jmh8231-Dev/agissat-hw-2025/docs/Ref/STM32H745XI 전원설계/.@__thumb/s800STM32H745 Powet supply scheme.PNG

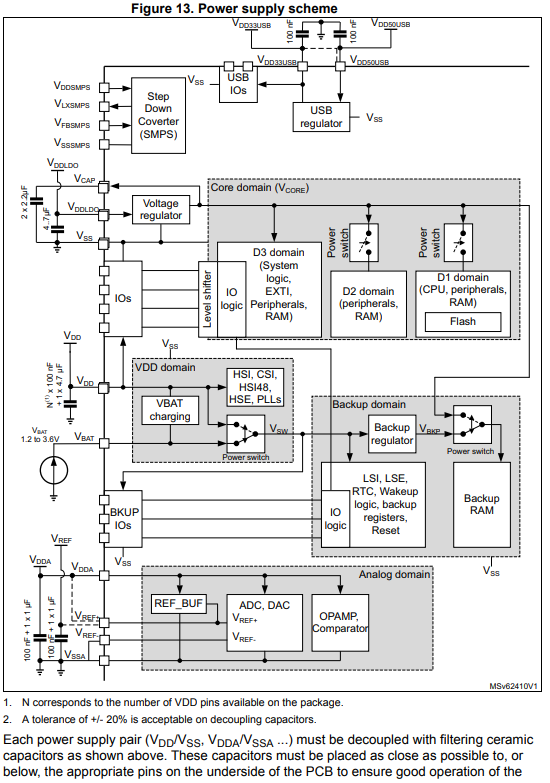
docs/Ref/STM32H745XI 전원설계/.@__thumb/s800STM32H745 Powet supply scheme.PNG
