jmh8231-Dev/agissat-hw-2025/RadCheck-SDRAM/Additional Parts.kicad_sch

## KiCad design RadCheck-SDRAM/Additional Parts.kicad_sch (2025-08-21)

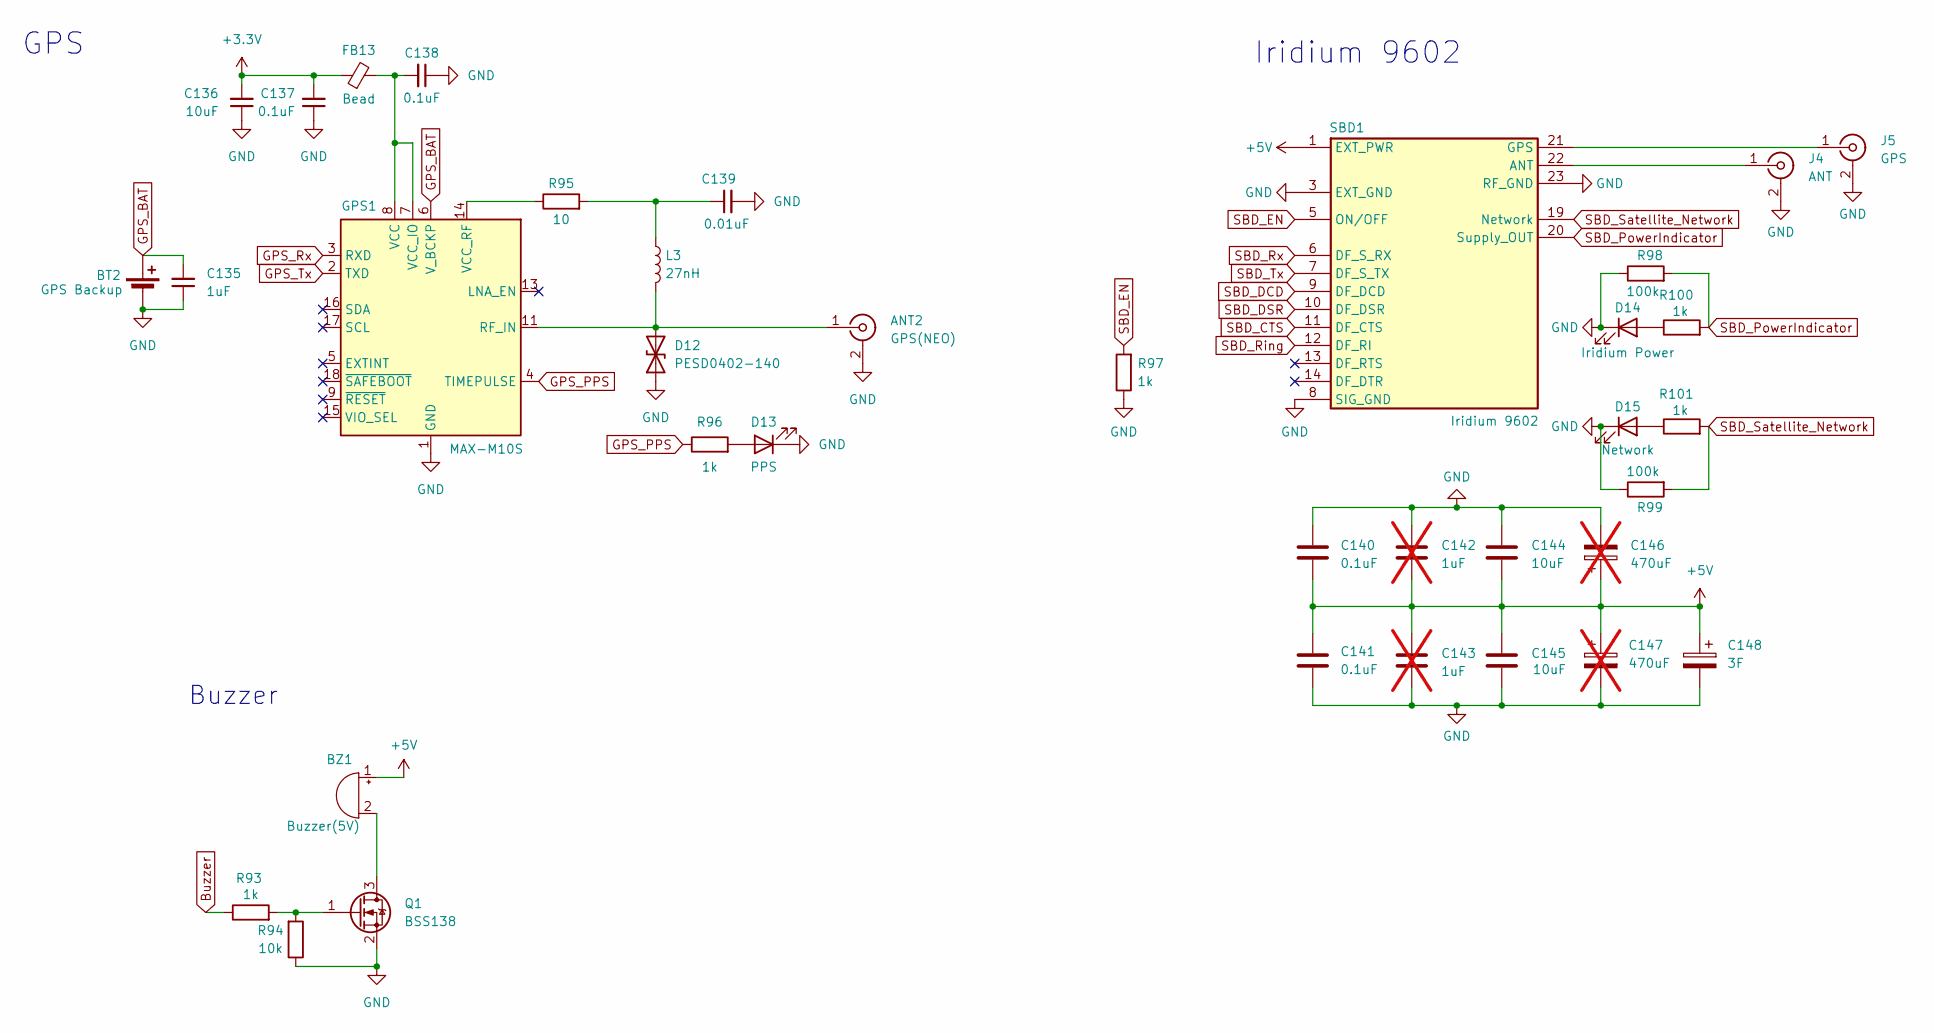
[picture p11: schematic Additional Parts.kicad_sch]

Parts:
ANT2: GPS(NEO); SMA_Amphenol_132134-11_Vertical
BT2: GPS Backup; BAT-HLD-001
BZ1: Buzzer(5V); Buzzer_12x9.5RM7.6
C135: 1uF; C_0805_2012Metric
C136: 10uF; C_1206_3216Metric
C137, C138, C140, C141: 0.1uF; C_0805_2012Metric
C139: 0.01uF; C_0805_2012Metric
C142, C143: 1uF; C_0805_2012Metric; not fitted
C144, C145: 10uF; C_1210_3225Metric
C146, C147: 470uF; MVG25WV470M; not fitted
C148: 3F; PTV-6R0H505-R
D12: PESD0402-140; D_0402_1005Metric_Pad0.77x0.64mm_HandSolder
D13: PPS; LED_0805_2012Metric
D14: Iridium Power; LED_0805_2012Metric
D15: Network; LED_0805_2012Metric
FB13: Bead; L_0805_2012Metric
GPS1: MAX-M10S; ublox_MAX
J4: ANT; SMA_Amphenol_132134-11_Vertical
J5: GPS; SMA_Amphenol_132134-11_Vertical
L3: 27nH; L_0805_2012Metric
Q1: BSS138; SOT-23
R93, R96, R97, R100, R101: 1k; R_0805_2012Metric
R94: 10k; R_0603_1608Metric
R95: 10; R_0805_2012Metric
R98, R99: 100k; R_0805_2012Metric
SBD1: Iridium 9602; Iridium_9602

Connections:
+3.3V: C136.2, C137.2, FB13.1
+5V: BZ1.1 (-), C140.2, C141.1, C142.2, C143.1, C144.2, C145.1, C146.1, C147.1, C148.1, SBD1.1 (EXT_PWR), SBD1.2 (EXT_PWR)
Buzzer: R93.1
GND: ANT2.2 (Ext), BT2.2 (-), C135.1, C136.1, C137.1, C138.1, C139.2, C140.1, C141.2, C142.1, C143.2, C144.1, C145.2, C146.2, C147.2, C148.2, D12.1 (A1), D13.1 (K), D14.1 (K), D15.1 (K), GPS1.1 (GND), GPS1.10 (GND), GPS1.12 (GND), J4.2 (Ext), J5.2 (Ext), Q1.2 (S), R94.1, R97.1, R98.1, R99.1, SBD1.3 (EXT_GND), SBD1.4 (EXT_GND), SBD1.8 (SIG_GND), SBD1.15 (SIG_GND), SBD1.18 (SIG_GND), SBD1.23 (RF_GND)
GPS_BAT: BT2.1 (+), C135.2, GPS1.6 (V_BCKP)
GPS_PPS: GPS1.4 (TIMEPULSE), R96.1
GPS_Rx: GPS1.3 (RXD)
GPS_Tx: GPS1.2 (TXD)
unnamed: ANT2.1 (In), D12.2 (A2), GPS1.11 (RF_IN), L3.2
unnamed: BZ1.2 (+), Q1.3 (D)
unnamed: C138.2, FB13.2, GPS1.7 (VCC_IO), GPS1.8 (VCC)
unnamed: C139.1, L3.1, R95.2
unnamed: D13.2 (A), R96.2
unnamed: D14.2 (A), R100.1
unnamed: D15.2 (A), R101.1
unnamed: GPS1.14 (VCC_RF), R95.1
unnamed: J4.1 (In), SBD1.22 (ANT)
unnamed: J5.1 (In), SBD1.21 (GPS)
unnamed: Q1.1 (G), R93.2, R94.2
SBD_CTS: SBD1.11 (DF_CTS)
SBD_DCD: SBD1.9 (DF_DCD)
SBD_DSR: SBD1.10 (DF_DSR)
SBD_EN: R97.2, SBD1.5 (ON/OFF)
SBD_PowerIndicator: R98.2, R100.2, SBD1.20 (Supply_OUT)
SBD_Ring: SBD1.12 (DF_RI)
SBD_Rx: SBD1.6 (DF_S_RX)
SBD_Satellite_Network: R99.2, R101.2, SBD1.19 (Network)
SBD_Tx: SBD1.7 (DF_S_TX)

Notes on the sheet:
Iridium 9602
Buzzer
GPS
