jmh8231-Dev/agissat-hw-2025/RadCheck-SDRAM/MCU.kicad_sch

## KiCad design RadCheck-SDRAM/MCU.kicad_sch (2025-08-21)

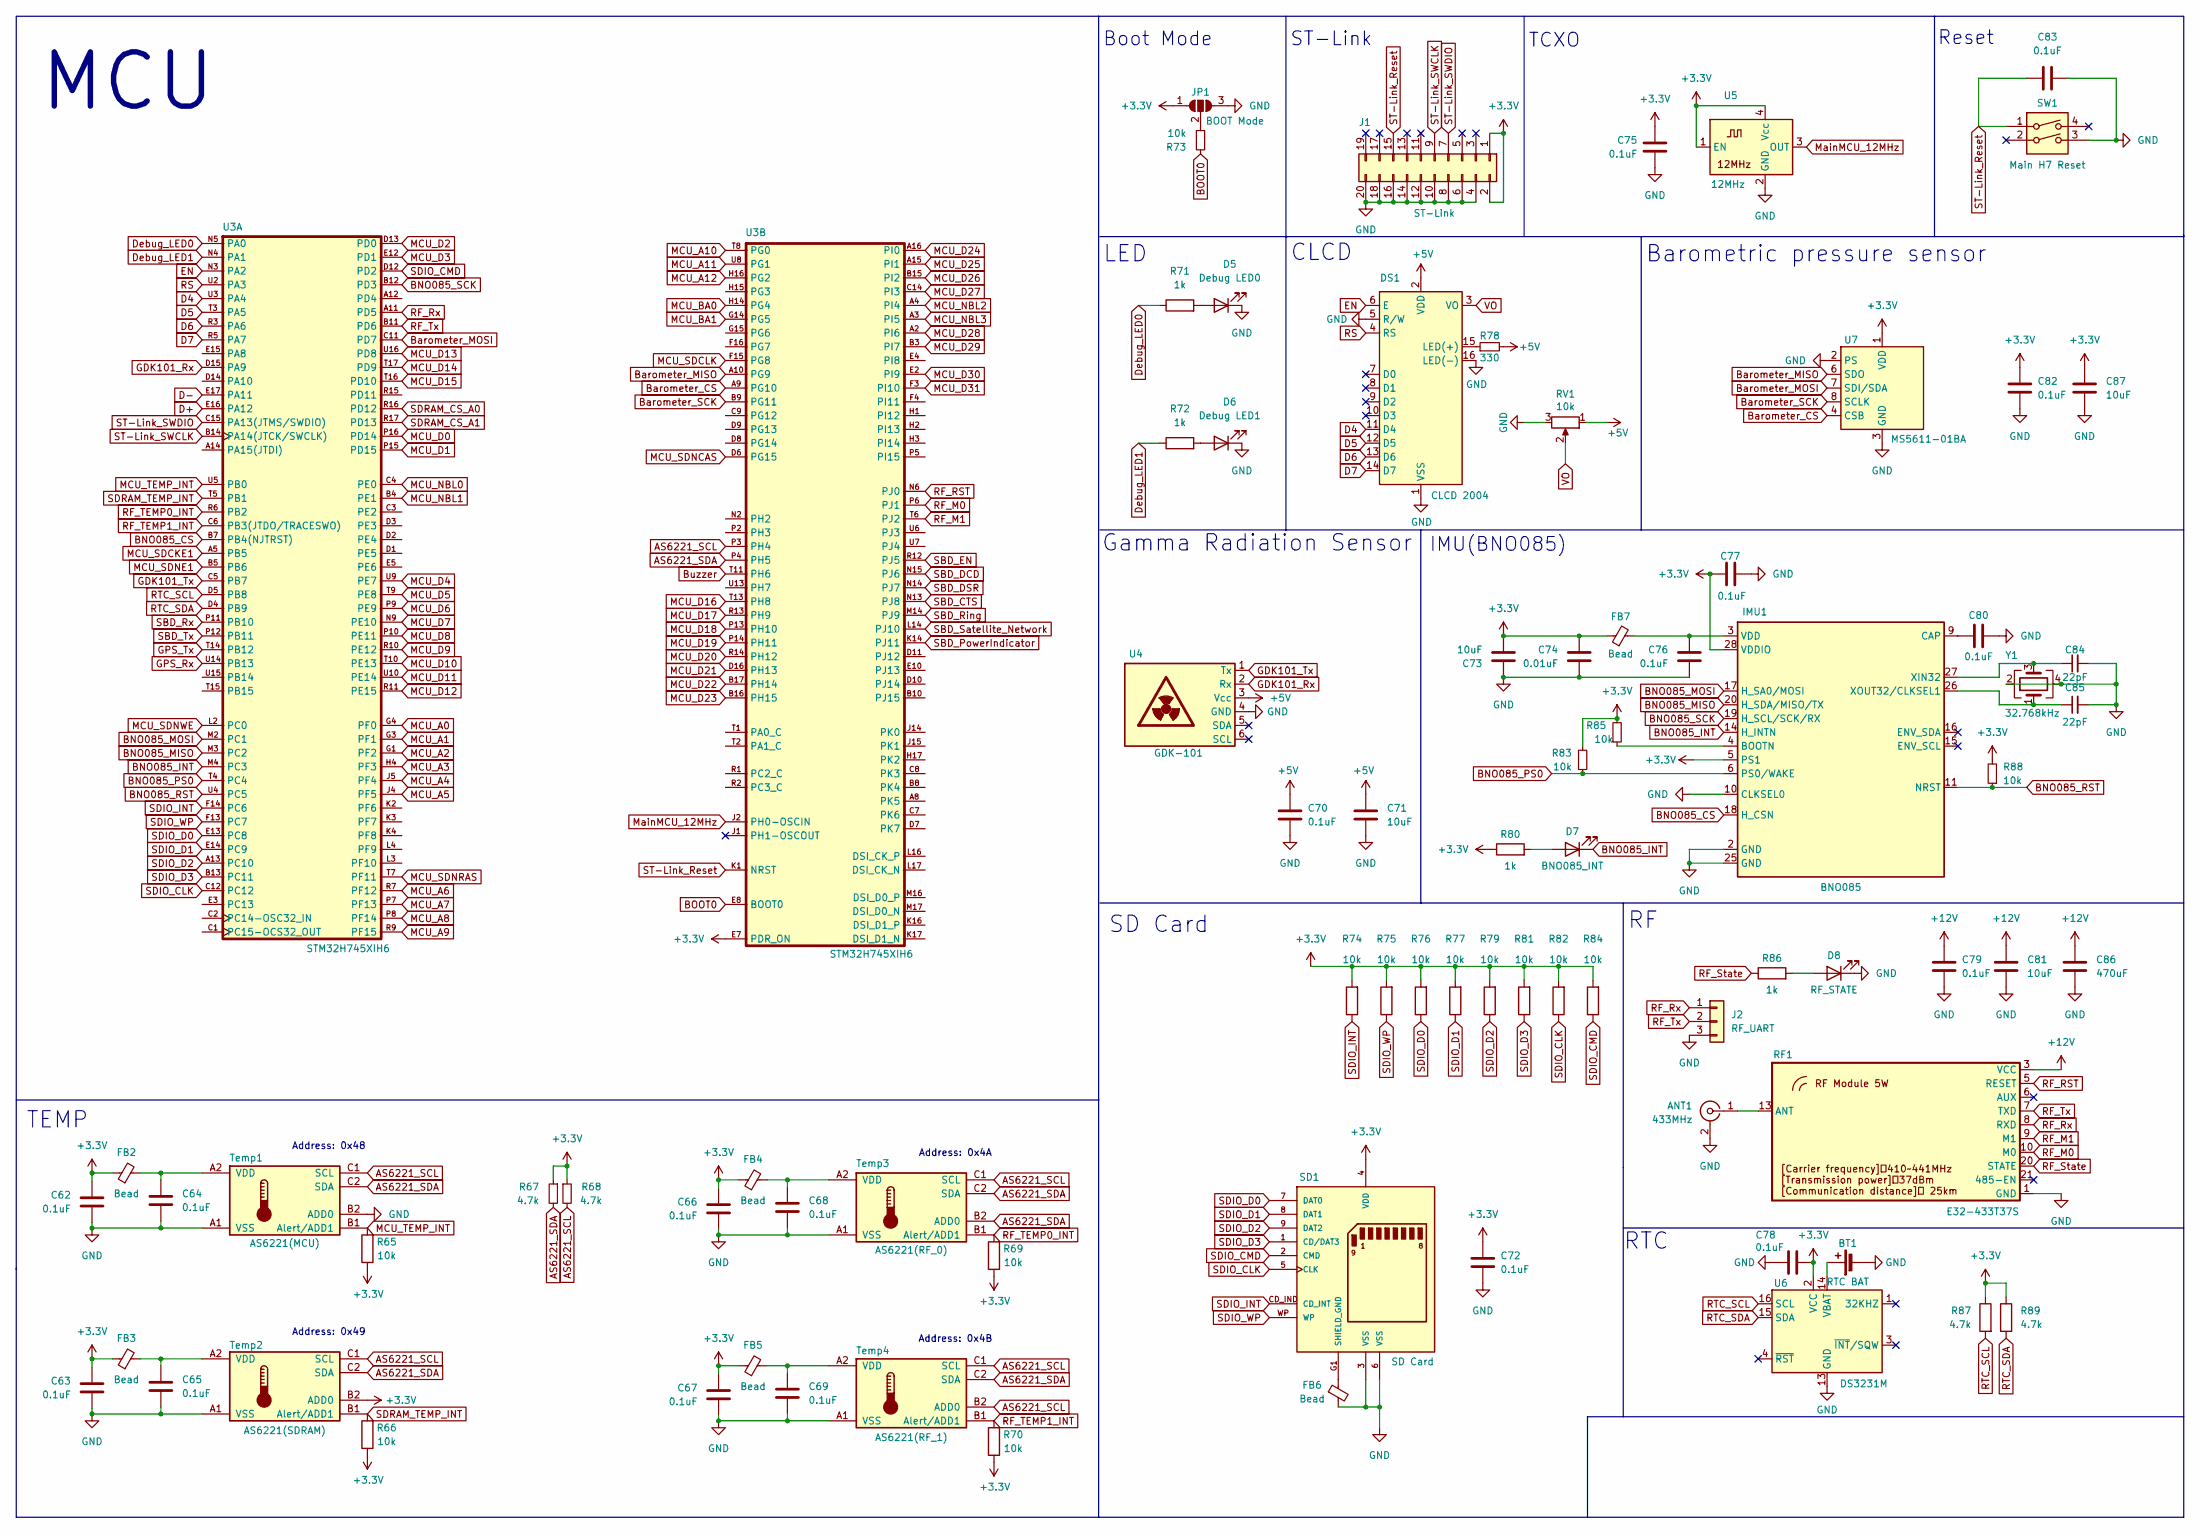
[picture p12: schematic MCU.kicad_sch]

Parts:
ANT1: 433MHz; SMA_Amphenol_132134-11_Vertical
BT1: RTC BAT; BAT-HLD-001
C62, C63, C64, C65, C66, C67, C68, C69, C70, C72, C75, C76, C77, C78, C79, C80, C82, C83: 0.1uF; C_0805_2012Metric
C71, C73, C81, C87: 10uF; C_1210_3225Metric
C74: 0.01uF; C_0805_2012Metric
C84, C85: 22pF; C_0805_2012Metric
C86: 470uF; MVG25WV470M
D5: Debug LED0; LED_0805_2012Metric
D6: Debug LED1; LED_0805_2012Metric
D7: BNO085_INT; LED_0805_2012Metric
D8: RF_STATE; LED_0805_2012Metric
DS1: CLCD 2004; LCD-20x4
FB2, FB3, FB4, FB5, FB6, FB7: Bead; L_0805_2012Metric
IMU1: BNO085; LGA-28_5.2x3.8mm_P0.5mm
J1: ST-Link; IDC-Header_2x10_P2.54mm_Vertical
J2: RF_UART; PinSocket_1x03_P2.54mm_Vertical
JP1: BOOT Mode; SolderJumper-3_P1.3mm_Open_RoundedPad1.0x1.5mm
R65, R66, R69, R70, R73, R74, R75, R76, R77, R79, R81, R82, R83, R84, R85, R88: 10k; R_0805_2012Metric
R67, R68, R87, R89: 4.7k; R_0805_2012Metric
R71, R72, R80, R86: 1k; R_0805_2012Metric
R78: 330; R_0805_2012Metric
RF1: E32-433T37S
RV1: 10k; 3362P-103LF
SD1: SD Card; AMPHENOL_GSD090012SEU; PARTREV E
SW1: Main H7 Reset; SW_SMD_IT-1107
Temp1: AS6221(MCU); WLCSP-6_1.4x1.0mm_P0.4mm
Temp2: AS6221(SDRAM); WLCSP-6_1.4x1.0mm_P0.4mm
Temp3: AS6221(RF_0); WLCSP-6_1.4x1.0mm_P0.4mm
Temp4: AS6221(RF_1); WLCSP-6_1.4x1.0mm_P0.4mm
U3: STM32H745XIH6; TFBGA-265_14x14mm_Layout17x17_P0.8mm
U4: GDK-101
U5: 12MHz; ECS-TXO-2016
U6: DS3231M; SOIC-16W_7.5x10.3mm_P1.27mm
U7: MS5611-01BA; LGA-8_3x5mm_P1.25mm
Y1: 32.768kHz; XC32M4

Connections:
+3.3V: C62.2, C63.2, C66.2, C67.2, C72.1, C73.1, C74.2, C75.1, C77.1, C78.2, C82.1, C87.1, FB2.1, FB3.1, FB4.1, FB5.1, FB7.1, IMU1.5 (PS1), IMU1.28 (VDDIO), J1.1, J1.2, JP1.1 (A), R65.1, R66.1, R67.1, R68.1, R69.1, R70.1, R74.2, R75.2, R76.2, R77.2, R79.2, R80.1, R81.2, R82.2, R83.2, R84.2, R85.2, R87.1, R88.2, R89.1, SD1.4 (VDD), Temp2.B2 (ADD0), U3.E7 (PDR_ON), U5.1 (EN), U5.4 (Vcc), U6.2 (VCC), U7.1 (VDD)
+5V: C70.1, C71.1, DS1.2 (VDD), R78.2, RV1.1, U4.3 (Vcc)
+12V: C79.1, C81.1, C86.1, RF1.3 (VCC), RF1.4 (VCC)
AS6221_SCL: R68.2, Temp1.C1 (SCL), Temp2.C1 (SCL), Temp3.C1 (SCL), Temp4.B2 (ADD0), Temp4.C1 (SCL), U3.P3 (PH4)
AS6221_SDA: R67.2, Temp1.C2 (SDA), Temp2.C2 (SDA), Temp3.B2 (ADD0), Temp3.C2 (SDA), Temp4.C2 (SDA), U3.P4 (PH5)
BNO085_CS: IMU1.18 (H_CSN), U3.B7 (PB4(NJTRST))
BNO085_INT: D7.1 (K), IMU1.14 (H_INTN), U3.M4 (PC3)
BNO085_MISO: IMU1.20 (H_SDA/MISO/TX), U3.M3 (PC2)
BNO085_MOSI: IMU1.17 (H_SA0/MOSI), U3.M2 (PC1)
BNO085_PS0: IMU1.6 (PS0/WAKE), R83.1, U3.T4 (PC4)
BNO085_RST: IMU1.11 (NRST), R88.1, U3.U4 (PC5)
BNO085_SCK: IMU1.19 (H_SCL/SCK/RX), U3.B12 (PD3)
BOOT0: R73.2, U3.E8 (BOOT0)
Barometer_CS: U3.A9 (PG10), U7.4 (CSB), U7.5 (CSB)
Barometer_MISO: U3.A10 (PG9), U7.6 (SDO)
Barometer_MOSI: U3.C11 (PD7), U7.7 (SDI/SDA)
Barometer_SCK: U3.B9 (PG11), U7.8 (SCLK)
Buzzer: U3.T11 (PH6)
D4: DS1.11 (D4), U3.U3 (PA4)
D5: DS1.12 (D5), U3.T3 (PA5)
D6: DS1.13 (D6), U3.R3 (PA6)
D7: DS1.14 (D7), U3.R5 (PA7)
D+: U3.E16 (PA12)
D-: U3.E17 (PA11)
Debug_LED0: R71.1, U3.N5 (PA0)
Debug_LED1: R72.1, U3.N4 (PA1)
EN: DS1.6 (E), U3.N3 (PA2)
GDK101_Rx: U3.D15 (PA9), U4.2 (Rx)
GDK101_Tx: U3.C5 (PB7), U4.1 (Tx)
GND: ANT1.2 (Ext), BT1.2 (-), C62.1, C63.1, C64.2, C65.2, C66.1, C67.1, C68.2, C69.2, C70.2, C71.2, C72.2, C73.2, C74.1, C75.2, C76.2, C77.2, C78.1, C79.2, C80.1, C81.2, C82.2, C83.2, C84.2, C85.2, C86.2, C87.2, D5.1 (K), D6.1 (K), D8.1 (K), DS1.1 (VSS), DS1.5 (R/W), DS1.16 (LED(-)), FB6.2, IMU1.2 (GND), IMU1.10 (CLKSEL0), IMU1.25 (GND), J1.4, J1.6, J1.8, J1.10, J1.12, J1.14, J1.16, J1.18, J1.20, J2.3, JP1.3 (B), RF1.1 (GND), RF1.2 (GND), RF1.11 (GND), RF1.12 (GND), RF1.14 (GND), RF1.15 (GND), RF1.16 (GND), RF1.17 (GND), RF1.18 (GND), RF1.19 (GND), RF1.27 (GND), RV1.3, SD1.3 (VSS), SD1.6 (VSS), SW1.3, Temp1.A1 (VSS), Temp1.B2 (ADD0), Temp2.A1 (VSS), Temp3.A1 (VSS), Temp4.A1 (VSS), U4.4 (GND), U5.2 (GND), U6.5 (GND), U6.6 (GND), U6.7 (GND), U6.8 (GND), U6.9 (GND), U6.10 (GND), U6.11 (GND), U6.12 (GND), U6.13 (GND), U7.2 (PS), U7.3 (GND), Y1.2, Y1.4
GPS_Rx: U3.U14 (PB13)
GPS_Tx: U3.T14 (PB12)
MCU_A0: U3.G4 (PF0)
MCU_A1: U3.G3 (PF1)
MCU_A2: U3.G1 (PF2)
MCU_A3: U3.H4 (PF3)
MCU_A4: U3.J5 (PF4)
MCU_A5: U3.J4 (PF5)
MCU_A6: U3.R7 (PF12)
MCU_A7: U3.P7 (PF13)
MCU_A8: U3.P8 (PF14)
MCU_A9: U3.R9 (PF15)
MCU_A10: U3.T8 (PG0)
MCU_A11: U3.U8 (PG1)
MCU_A12: U3.H16 (PG2)
MCU_BA0: U3.H14 (PG4)
MCU_BA1: U3.G14 (PG5)
MCU_D0: U3.P16 (PD14)
MCU_D1: U3.P15 (PD15)
MCU_D2: U3.D13 (PD0)
MCU_D3: U3.E12 (PD1)
MCU_D4: U3.U9 (PE7)
MCU_D5: U3.T9 (PE8)
MCU_D6: U3.P9 (PE9)
MCU_D7: U3.N9 (PE10)
MCU_D8: U3.P10 (PE11)
MCU_D9: U3.R10 (PE12)
MCU_D10: U3.T10 (PE13)
MCU_D11: U3.U10 (PE14)
MCU_D12: U3.R11 (PE15)
MCU_D13: U3.U16 (PD8)
MCU_D14: U3.T17 (PD9)
MCU_D15: U3.T16 (PD10)
MCU_D16: U3.T13 (PH8)
MCU_D17: U3.R13 (PH9)
MCU_D18: U3.P13 (PH10)
MCU_D19: U3.P14 (PH11)
MCU_D20: U3.R14 (PH12)
MCU_D21: U3.D16 (PH13)
MCU_D22: U3.B17 (PH14)
MCU_D23: U3.B16 (PH15)
MCU_D24: U3.A16 (PI0)
MCU_D25: U3.A15 (PI1)
MCU_D26: U3.B15 (PI2)
MCU_D27: U3.C14 (PI3)
MCU_D28: U3.A2 (PI6)
MCU_D29: U3.B3 (PI7)
MCU_D30: U3.E2 (PI9)
MCU_D31: U3.F3 (PI10)
MCU_NBL0: U3.C4 (PE0)
MCU_NBL1: U3.B4 (PE1)
MCU_NBL2: U3.A4 (PI4)
MCU_NBL3: U3.A3 (PI5)
MCU_SDCKE1: U3.A5 (PB5)
MCU_SDCLK: U3.F15 (PG8)
MCU_SDNCAS: U3.D6 (PG15)
MCU_SDNE1: U3.B5 (PB6)
MCU_SDNRAS: U3.T7 (PF11)
MCU_SDNWE: U3.L2 (PC0)
MCU_TEMP_INT: R65.2, Temp1.B1 (Alert/ADD1), U3.U5 (PB0)
MainMCU_12MHz: U3.J2 (PH0-OSCIN), U5.3 (OUT)
unnamed: ANT1.1 (In), RF1.13 (ANT)
unnamed: BT1.1 (+), U6.14 (VBAT)
unnamed: C64.1, FB2.2, Temp1.A2 (VDD)
unnamed: C65.1, FB3.2, Temp2.A2 (VDD)
unnamed: C68.1, FB4.2, Temp3.A2 (VDD)
unnamed: C69.1, FB5.2, Temp4.A2 (VDD)
unnamed: C76.1, FB7.2, IMU1.3 (VDD)
unnamed: C80.2, IMU1.9 (CAP)
unnamed: C84.1, IMU1.27 (XIN32), Y1.3
unnamed: C85.1, IMU1.26 (XOUT32/CLKSEL1), Y1.1
unnamed: D5.2 (A), R71.2
unnamed: D6.2 (A), R72.2
unnamed: D7.2 (A), R80.2
unnamed: D8.2 (A), R86.2
unnamed: DS1.15 (LED(+)), R78.1
unnamed: FB6.1, SD1.G1 (SHIELD_GND), SD1.G2 (SHIELD_GND), SD1.G3 (SHIELD_GND), SD1.G4 (SHIELD_GND)
unnamed: IMU1.4 (BOOTN), R85.1
unnamed: JP1.2 (C), R73.1
RF_M0: RF1.10 (M0), U3.P6 (PJ1)
RF_M1: RF1.9 (M1), U3.T6 (PJ2)
RF_RST: RF1.5 (RESET), U3.N6 (PJ0)
RF_Rx: J2.1, RF1.8 (RXD), U3.A11 (PD5)
RF_State: R86.1, RF1.20 (STATE)
RF_TEMP0_INT: R69.2, Temp3.B1 (Alert/ADD1), U3.R6 (PB2)
RF_TEMP1_INT: R70.2, Temp4.B1 (Alert/ADD1), U3.C6 (PB3(JTDO/TRACESWO))
RF_Tx: J2.2, RF1.7 (TXD), U3.B11 (PD6)
RS: DS1.4 (RS), U3.U2 (PA3)
RTC_SCL: R87.2, U3.D5 (PB8), U6.16 (SCL)
RTC_SDA: R89.2, U3.D4 (PB9), U6.15 (SDA)
SBD_CTS: U3.N13 (PJ8)
SBD_DCD: U3.N15 (PJ6)
SBD_DSR: U3.N14 (PJ7)
SBD_EN: U3.R12 (PJ5)
SBD_PowerIndicator: U3.K14 (PJ11)
SBD_Ring: U3.M14 (PJ9)
SBD_Rx: U3.P11 (PB10)
SBD_Satellite_Network: U3.L14 (PJ10)
SBD_Tx: U3.P12 (PB11)
SDIO_CLK: R82.1, SD1.5 (CLK), U3.C12
SDIO_CMD: R84.1, SD1.2 (CMD), U3.D12 (PD2)
SDIO_D0: R76.1, SD1.7 (DAT0), U3.E13 (PC8)
SDIO_D1: R77.1, SD1.8 (DAT1), U3.E14 (PC9)
SDIO_D2: R79.1, SD1.9 (DAT2), U3.A13 (PC10)
SDIO_D3: R81.1, SD1.1 (CD/DAT3), U3.B13 (PC11)
SDIO_INT: R74.1, SD1.CD_IND (CD_INT), U3.F14 (PC6)
SDIO_WP: R75.1, SD1.WP, U3.F13 (PC7)
SDRAM_CS_A0: U3.R16 (PD12)
SDRAM_CS_A1: U3.R17 (PD13)
SDRAM_TEMP_INT: R66.2, Temp2.B1 (Alert/ADD1), U3.T5 (PB1)
ST-Link_Reset: C83.1, J1.15, SW1.1, U3.K1 (NRST)
ST-Link_SWCLK: J1.9, U3.B14 (PA14(JTCK/SWCLK))
ST-Link_SWDIO: J1.7, U3.C15 (PA13(JTMS/SWDIO))
VO: DS1.3 (VO), RV1.2

Notes on the sheet:
TCXO
ST-Link
Address: 0x4B
RTC
Boot Mode
CLCD
MCU
Gamma Radiation Sensor
Reset
IMU(BNO085)
Barometric pressure sensor
Address: 0x49
Address: 0x48
LED
TEMP
Address: 0x4A
SD Card
