jmh8231-Dev/agissat-hw-2025/RadCheck-SDRAM/Power.kicad_sch

## KiCad design RadCheck-SDRAM/Power.kicad_sch (2025-08-21)

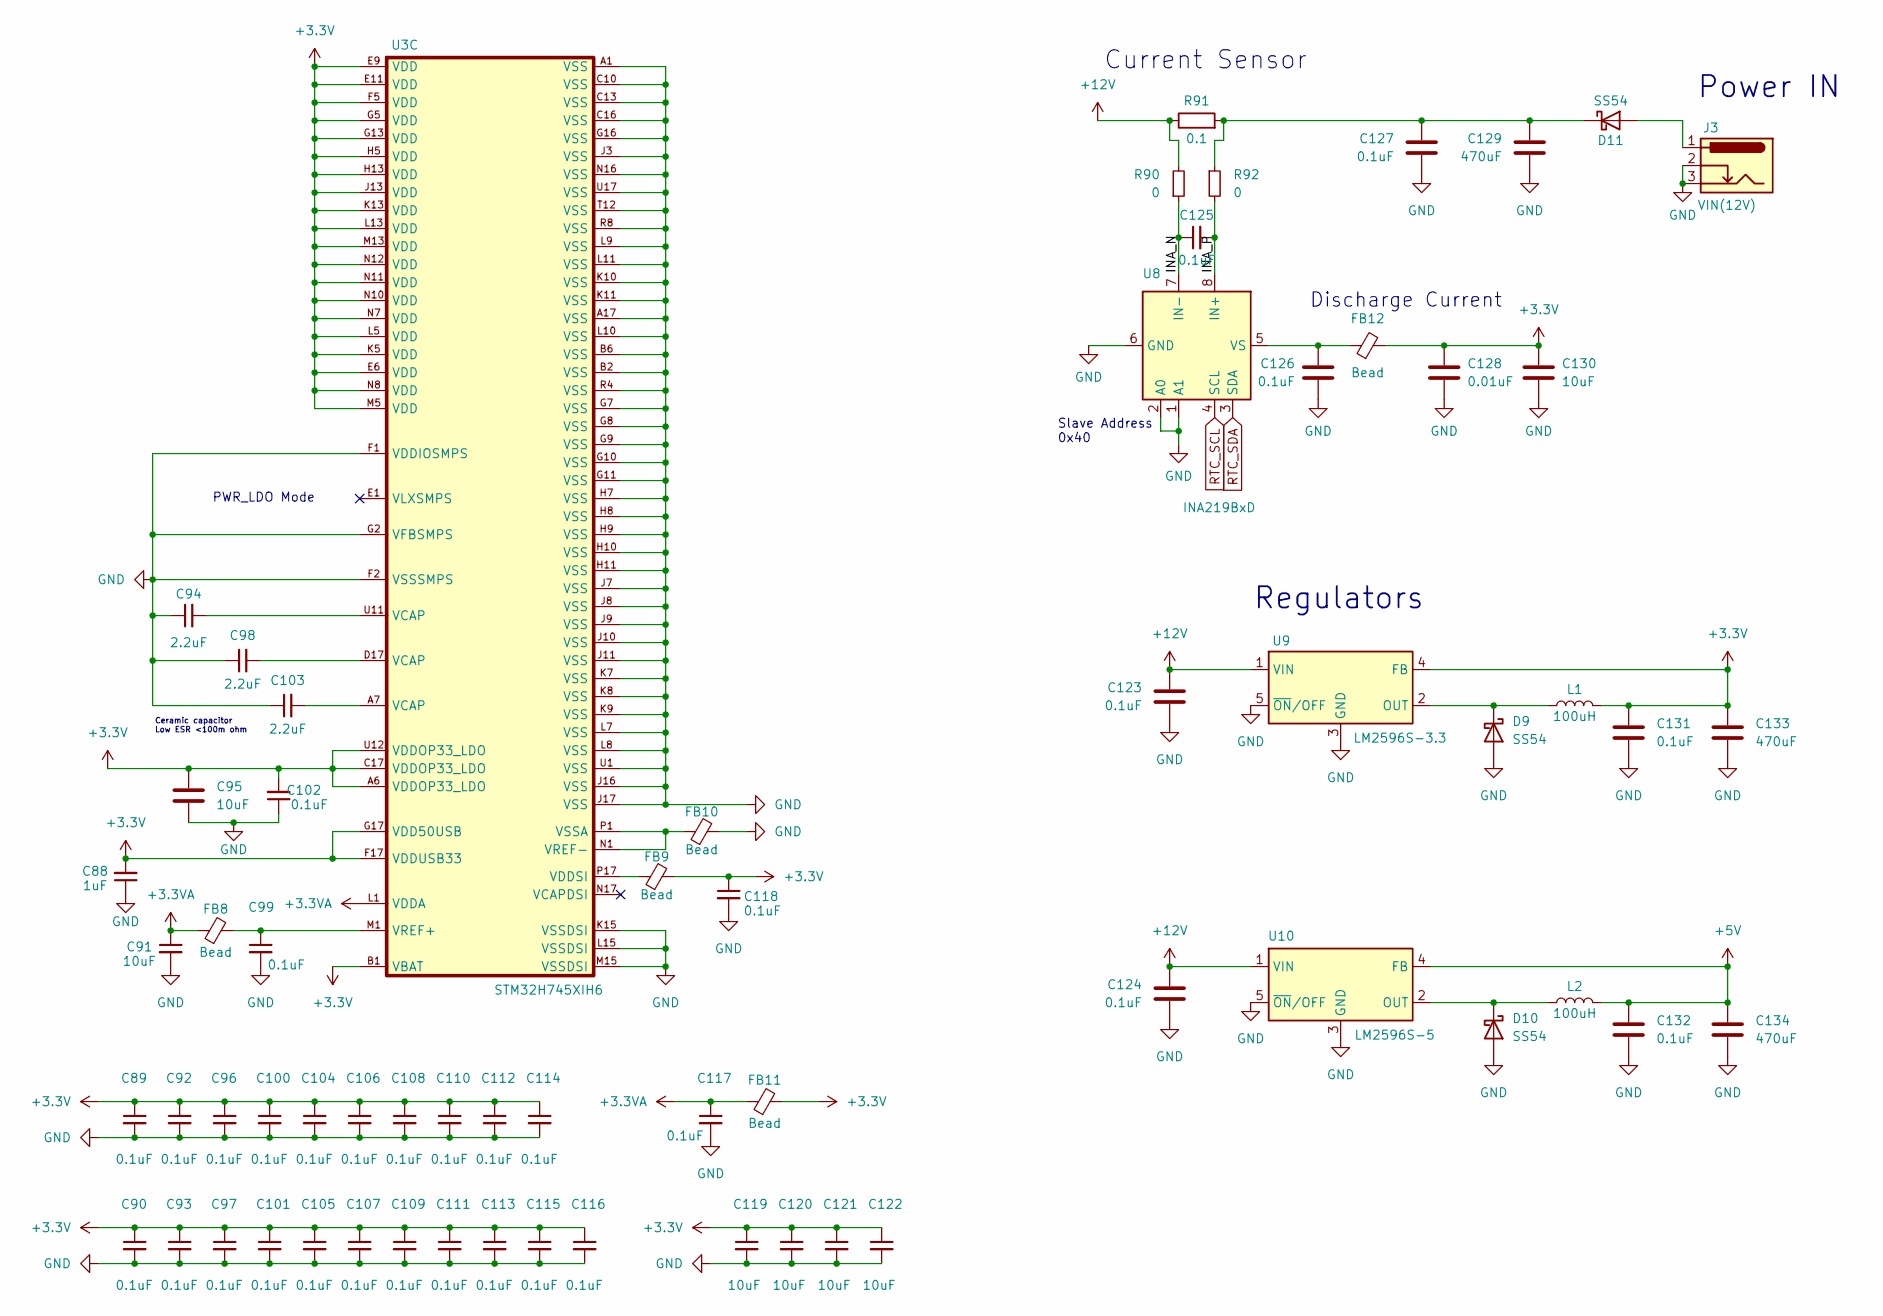
[picture p13: schematic Power.kicad_sch]

Parts:
C88: 1uF; C_0805_2012Metric
C89, C90, C92, C93, C96, C97, C99, C100, C101, C102, C104, C105, C106, C107, C108, C109, C110, C111, C112, C113, C114, C115, C116, C117, C118, C123, C124, C125, C126, C127, C131, C132: 0.1uF; C_0805_2012Metric
C91, C95, C119, C120, C121, C122, C130: 10uF; C_1210_3225Metric
C94, C98, C103: 2.2uF; C_0805_2012Metric
C128: 0.01uF; C_0805_2012Metric
C129, C133, C134: 470uF; MVG25WV470M
D9, D10, D11: SS54; D_SMC
FB8, FB9, FB10, FB11, FB12: Bead; L_0805_2012Metric
J3: VIN(12V); BarrelJack_Horizontal
L1, L2: 100uH; L_12x12mm_H8mm
R90, R92: 0; R_0805_2012Metric
R91: 0.1; TO-126-2_Horizontal_TabDown
U3: STM32H745XIH6; TFBGA-265_14x14mm_Layout17x17_P0.8mm
U8: INA219BxD; SOIC-8_3.9x4.9mm_P1.27mm
U9: LM2596S-3.3; TO-263-5_TabPin3
U10: LM2596S-5; TO-263-5_TabPin3

Connections:
+3.3V: C88.2, C89.1, C90.1, C92.1, C93.1, C95.2, C96.1, C97.1, C100.1, C101.1, C102.2, C104.1, C105.1, C106.1, C107.1, C108.1, C109.1, C110.1, C111.1, C112.1, C113.1, C114.1, C115.1, C116.1, C118.1, C119.1, C120.1, C121.1, C122.1, C128.1, C130.1, C131.1, C133.1, FB9.2, FB11.2, FB12.2, L1.2, U3.A6 (VDDOP33_LDO), U3.B1 (VBAT), U3.C17 (VDDOP33_LDO), U3.E6 (VDD), U3.E9 (VDD), U3.E11 (VDD), U3.F5 (VDD), U3.F17 (VDDUSB33), U3.G5 (VDD), U3.G13 (VDD), U3.G17 (VDD50USB), U3.H5 (VDD), U3.H13 (VDD), U3.J13 (VDD), U3.K5 (VDD), U3.K13 (VDD), U3.L5 (VDD), U3.L13 (VDD), U3.M5 (VDD), U3.M13 (VDD), U3.N7 (VDD), U3.N8 (VDD), U3.N10 (VDD), U3.N11 (VDD), U3.N12 (VDD), U3.U12 (VDDOP33_LDO), U9.4 (FB)
+3.3VA: C91.1, C117.1, FB8.1, FB11.1, U3.L1 (VDDA)
+5V: C132.1, C134.1, L2.2, U10.4 (FB)
+12V: C123.1, C124.1, R90.2, R91.1, U9.1 (VIN), U10.1 (VIN)
GND: C88.1, C89.2, C90.2, C91.2, C92.2, C93.2, C94.1, C95.1, C96.2, C97.2, C98.1, C99.2, C100.2, C101.2, C102.1, C103.1, C104.2, C105.2, C106.2, C107.2, C108.2, C109.2, C110.2, C111.2, C112.2, C113.2, C114.2, C115.2, C116.2, C117.2, C118.2, C119.2, C120.2, C121.2, C122.2, C123.2, C124.2, C126.2, C127.2, C128.2, C129.2, C130.2, C131.2, C132.2, C133.2, C134.2, D9.2 (A), D10.2 (A), FB10.2, J3.2, J3.3, U3.A1 (VSS), U3.A17 (VSS), U3.B2 (VSS), U3.B6 (VSS), U3.C10 (VSS), U3.C13 (VSS), U3.C16 (VSS), U3.F1 (VDDIOSMPS), U3.F2 (VSSSMPS), U3.G2 (VFBSMPS), U3.G7 (VSS), U3.G8 (VSS), U3.G9 (VSS), U3.G10 (VSS), U3.G11 (VSS), U3.G16 (VSS), U3.H7 (VSS), U3.H8 (VSS), U3.H9 (VSS), U3.H10 (VSS), U3.H11 (VSS), U3.J3 (VSS), U3.J7 (VSS), U3.J8 (VSS), U3.J9 (VSS), U3.J10 (VSS), U3.J11 (VSS), U3.J16 (VSS), U3.J17 (VSS), U3.K7 (VSS), U3.K8 (VSS), U3.K9 (VSS), U3.K10 (VSS), U3.K11 (VSS), U3.K15 (VSSDSI), U3.L7 (VSS), U3.L8 (VSS), U3.L9 (VSS), U3.L10 (VSS), U3.L11 (VSS), U3.L15 (VSSDSI), U3.M15 (VSSDSI), U3.N16 (VSS), U3.R4 (VSS), U3.R8 (VSS), U3.T12 (VSS), U3.U1 (VSS), U3.U17 (VSS), U8.1 (A1), U8.2 (A0), U8.6 (GND), U9.3 (GND), U9.5 (~ON/OFF), U10.3 (GND), U10.5 (~ON/OFF)
INA_N: C125.1, R90.1, U8.7 (IN-)
INA_P: C125.2, R92.2, U8.8 (IN+)
unnamed: C94.2, U3.U11 (VCAP)
unnamed: C98.2, U3.D17 (VCAP)
unnamed: C99.1, FB8.2, U3.M1 (VREF+)
unnamed: C103.2, U3.A7 (VCAP)
unnamed: C126.1, FB12.1, U8.5 (VS)
unnamed: C127.1, C129.1, D11.1 (K), R91.2, R92.1
unnamed: D9.1 (K), L1.1, U9.2 (OUT)
unnamed: D10.1 (K), L2.1, U10.2 (OUT)
unnamed: D11.2 (A), J3.1
unnamed: FB9.1, U3.P17 (VDDSI)
unnamed: FB10.1, U3.N1 (VREF-), U3.P1 (VSSA)
RTC_SCL: U8.4 (SCL)
RTC_SDA: U8.3 (SDA)

Notes on the sheet:
Slave Address 0x40
Current Sensor
Discharge Current
Regulators
Power IN
PWR_LDO Mode
Ceramic capacitor Low ESR <100m ohm
