jmh8231-Dev/agissat-hw-2025/RadCheck-SDRAM/RadCheck-SDRAM.kicad_sch

## KiCad design RadCheck-SDRAM/RadCheck-SDRAM.kicad_sch (2025-08-21)

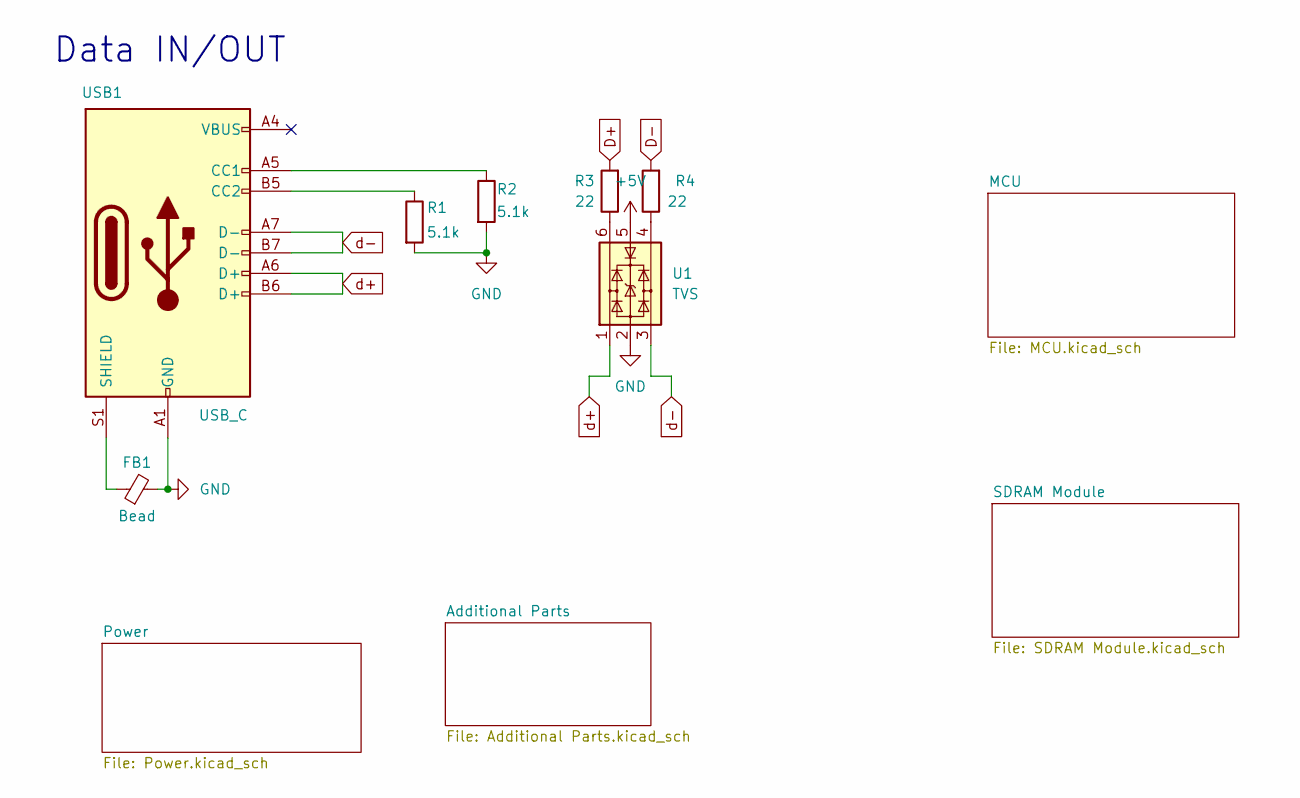
[picture p14: schematic RadCheck-SDRAM.kicad_sch]

Parts:
FB1: Bead; L_0805_2012Metric
R1, R2: 5.1k; R_0805_2012Metric
R3, R4: 22; R_0805_2012Metric
U1: TVS; SOT-23-6
USB1: USB_C; USB_C_Receptacle_HRO_TYPE-C-31-M-12

Connections:
+5V: U1.5
D+: R3.2, U1.1, USB1.A6 (D+), USB1.B6 (D+)
GND: FB1.2, R1.2, R2.2, U1.2, USB1.A1 (GND), USB1.A12 (GND), USB1.B1 (GND), USB1.B12 (GND)
unnamed: FB1.1, USB1.S1 (SHIELD)
unnamed: R1.1, USB1.B5 (CC2)
unnamed: R2.1, USB1.A5 (CC1)
unnamed: R3.1, U1.6
unnamed: R4.1, U1.4
unnamed: USB1.A4 (VBUS), USB1.A9 (VBUS), USB1.B4 (VBUS), USB1.B9 (VBUS)
d-: R4.2, U1.3, USB1.A7 (D-), USB1.B7 (D-)

Notes on the sheet:
Data IN/OUT
