jmh8231-Dev/agissat-hw-2025/RadCheck-SDRAM/SDRAM Module.kicad_sch

## KiCad design RadCheck-SDRAM/SDRAM Module.kicad_sch (2025-08-21)

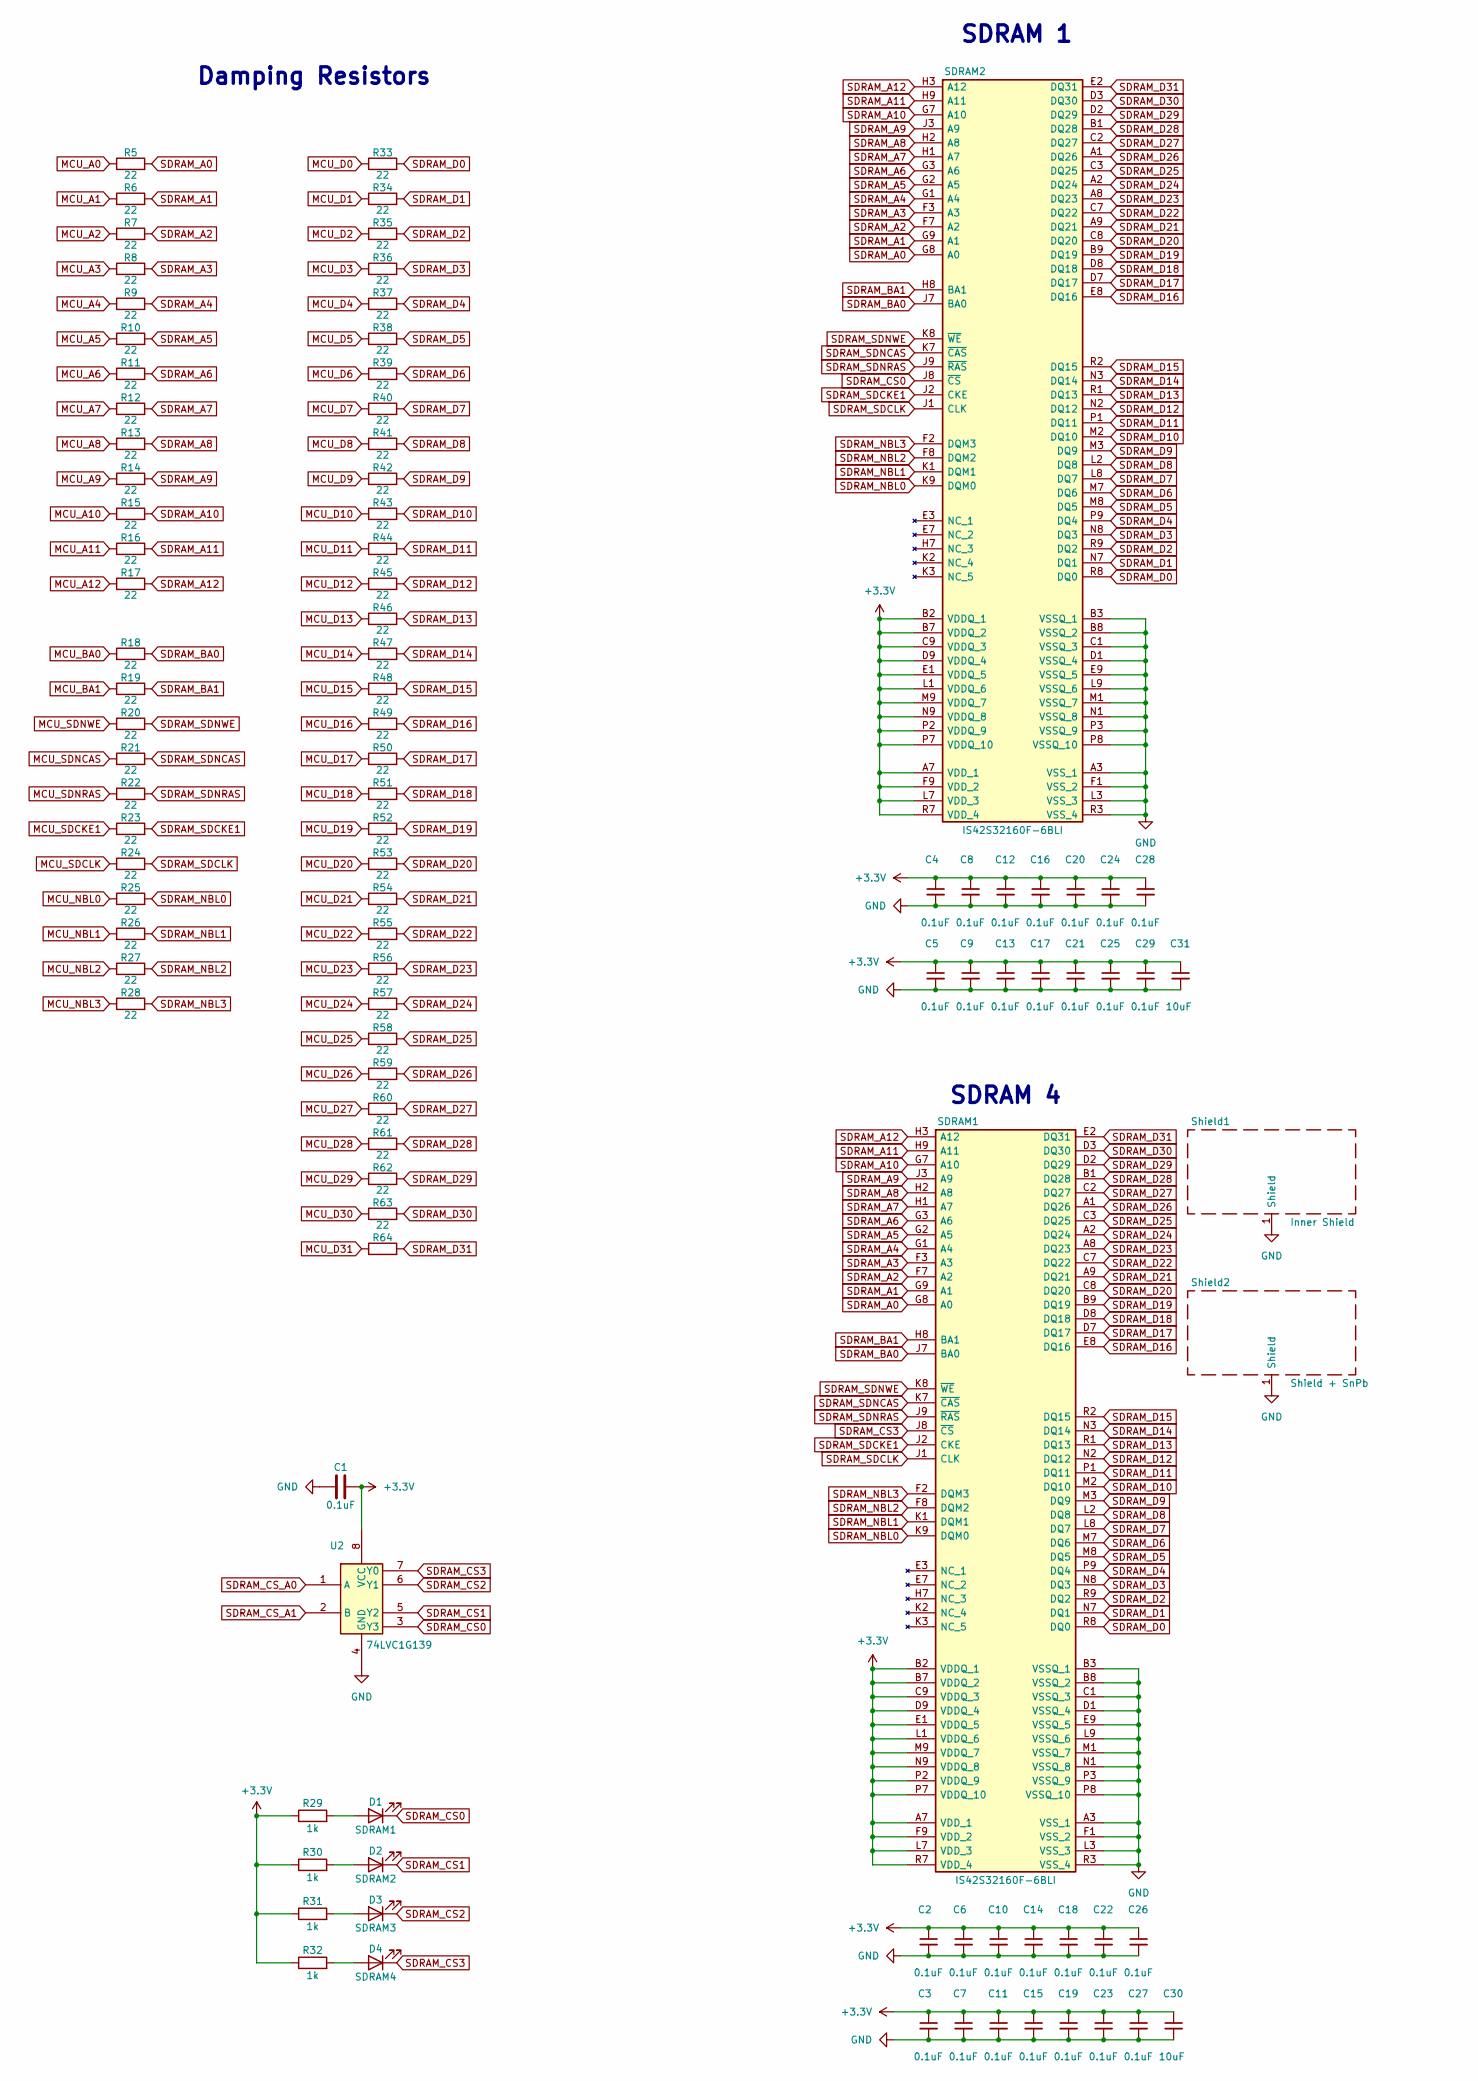
[picture p15: schematic SDRAM Module.kicad_sch, part in row 1, column 1]

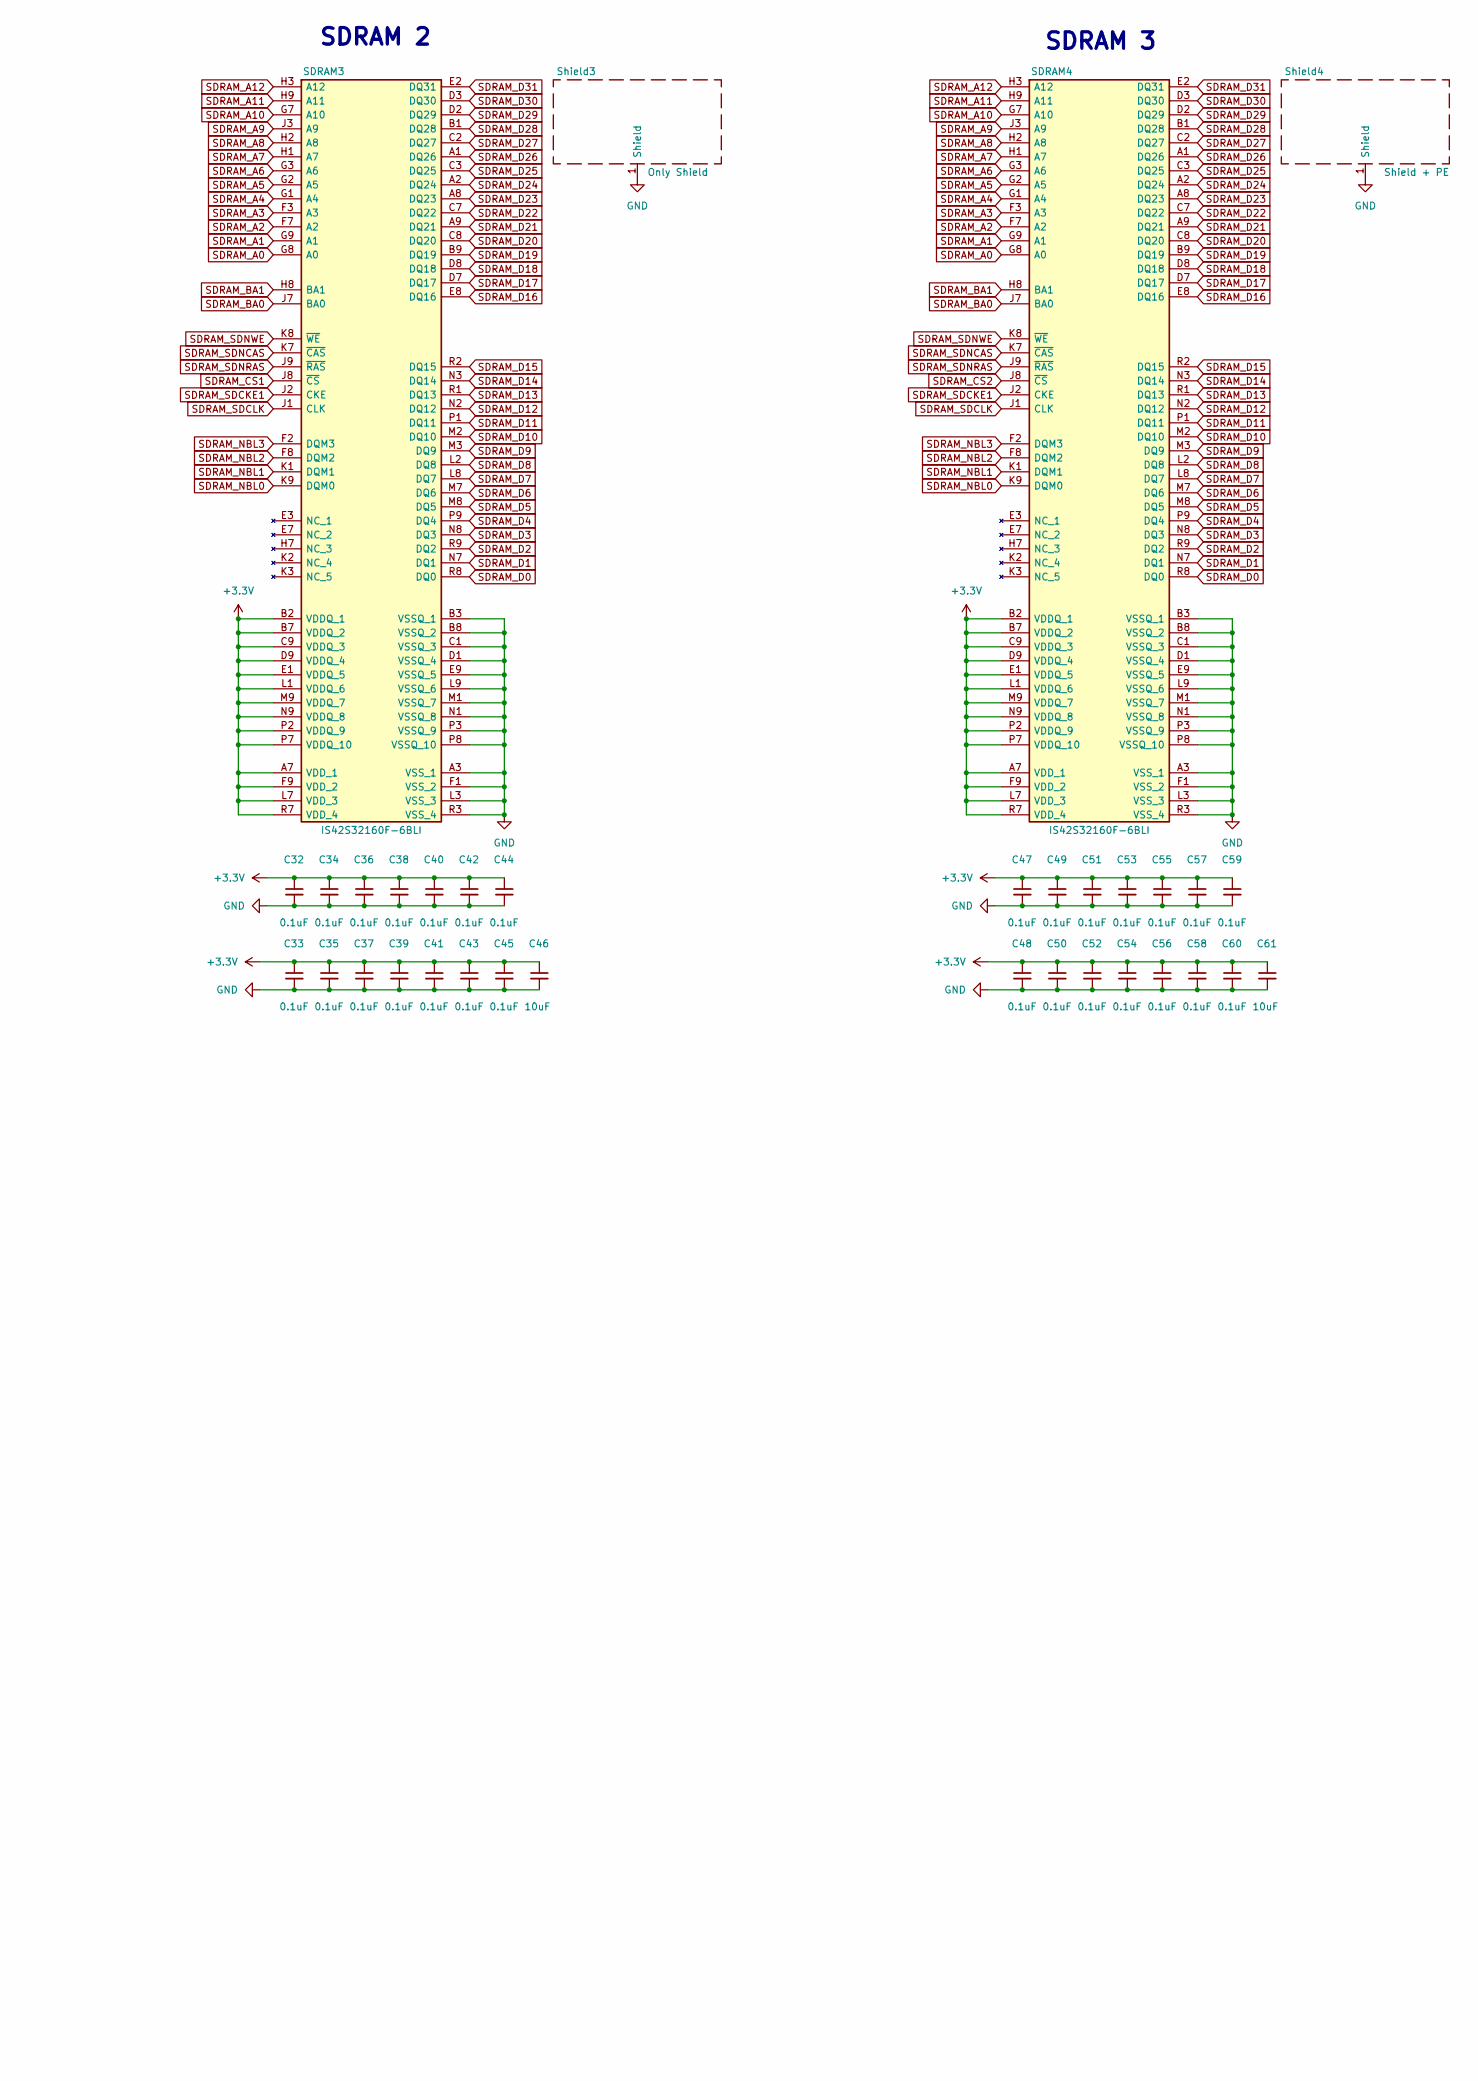
[picture p16: schematic SDRAM Module.kicad_sch, part in row 1, column 2]

Parts:
C1, C2, C3, C4, C5, C6, C7, C8, C9, C10, C11, C12, C13, C14, C15, C16, C17, C18, C19, C20, C21, C22, C23, C24, C25, C26, C27, C28, C29, C32, C33, C34, C35, C36, C37, C38, C39, C40, C41, C42, C43, C44, C45, C47, C48, C49, C50, C51, C52, C53, C54, C55, C56, C57, C58, C59, C60: 0.1uF; C_0805_2012Metric
C30, C31, C46, C61: 10uF; C_1210_3225Metric
D1: SDRAM1; LED_0805_2012Metric
D2: SDRAM2; LED_0805_2012Metric
D3: SDRAM3; LED_0805_2012Metric
D4: SDRAM4; LED_0805_2012Metric
R5, R6, R7, R8, R9, R10, R11, R12, R13, R14, R15, R16, R17, R18, R19, R20, R21, R22, R23, R24, R25, R26, R27, R28, R33, R34, R35, R36, R37, R38, R39, R40, R41, R42, R43, R44, R45, R46, R47, R48, R49, R50, R51, R52, R53, R54, R55, R56, R57, R58, R59, R60, R61, R62, R63, R64: 22; R_0402_1005Metric
R29, R30, R31, R32: 1k; R_0805_2012Metric
SDRAM1, SDRAM2, SDRAM3, SDRAM4: IS42S32160F-6BLI; BGA-90_8.0x13.0mm_Layout2x3x15_P0.8mm; Manufacturer_Part_Number IS42S32160F-6BLI
Shield1: Inner Shield; WE-SHC_ONE-PIECE_36903205S
Shield2: Shield + SnPb; MS257-10F
Shield3: Only Shield; WE-SHC_ONE-PIECE_36903205S
Shield4: Shield + PE; WE-SHC_SMD-FRAME_36103205S
U2: 74LVC1G139; Texas_DSBGA-8_0.9x1.9mm_Layout2x4_P0.5mm

Connections:
+3.3V: C1.2, C2.1, C3.1, C4.1, C5.1, C6.1, C7.1, C8.1, C9.1, C10.1, C11.1, C12.1, C13.1, C14.1, C15.1, C16.1, C17.1, C18.1, C19.1, C20.1, C21.1, C22.1, C23.1, C24.1, C25.1, C26.1, C27.1, C28.1, C29.1, C30.1, C31.1, C32.1, C33.1, C34.1, C35.1, C36.1, C37.1, C38.1, C39.1, C40.1, C41.1, C42.1, C43.1, C44.1, C45.1, C46.1, C47.1, C48.1, C49.1, C50.1, C51.1, C52.1, C53.1, C54.1, C55.1, C56.1, C57.1, C58.1, C59.1, C60.1, C61.1, R29.1, R30.1, R31.1, R32.1, SDRAM1.A7 (VDD_1), SDRAM1.B2 (VDDQ_1), SDRAM1.B7 (VDDQ_2), SDRAM1.C9 (VDDQ_3), SDRAM1.D9 (VDDQ_4), SDRAM1.E1 (VDDQ_5), SDRAM1.F9 (VDD_2), SDRAM1.L1 (VDDQ_6), SDRAM1.L7 (VDD_3), SDRAM1.M9 (VDDQ_7), SDRAM1.N9 (VDDQ_8), SDRAM1.P2 (VDDQ_9), SDRAM1.P7 (VDDQ_10), SDRAM1.R7 (VDD_4), SDRAM2.A7 (VDD_1), SDRAM2.B2 (VDDQ_1), SDRAM2.B7 (VDDQ_2), SDRAM2.C9 (VDDQ_3), SDRAM2.D9 (VDDQ_4), SDRAM2.E1 (VDDQ_5), SDRAM2.F9 (VDD_2), SDRAM2.L1 (VDDQ_6), SDRAM2.L7 (VDD_3), SDRAM2.M9 (VDDQ_7), SDRAM2.N9 (VDDQ_8), SDRAM2.P2 (VDDQ_9), SDRAM2.P7 (VDDQ_10), SDRAM2.R7 (VDD_4), SDRAM3.A7 (VDD_1), SDRAM3.B2 (VDDQ_1), SDRAM3.B7 (VDDQ_2), SDRAM3.C9 (VDDQ_3), SDRAM3.D9 (VDDQ_4), SDRAM3.E1 (VDDQ_5), SDRAM3.F9 (VDD_2), SDRAM3.L1 (VDDQ_6), SDRAM3.L7 (VDD_3), SDRAM3.M9 (VDDQ_7), SDRAM3.N9 (VDDQ_8), SDRAM3.P2 (VDDQ_9), SDRAM3.P7 (VDDQ_10), SDRAM3.R7 (VDD_4), SDRAM4.A7 (VDD_1), SDRAM4.B2 (VDDQ_1), SDRAM4.B7 (VDDQ_2), SDRAM4.C9 (VDDQ_3), SDRAM4.D9 (VDDQ_4), SDRAM4.E1 (VDDQ_5), SDRAM4.F9 (VDD_2), SDRAM4.L1 (VDDQ_6), SDRAM4.L7 (VDD_3), SDRAM4.M9 (VDDQ_7), SDRAM4.N9 (VDDQ_8), SDRAM4.P2 (VDDQ_9), SDRAM4.P7 (VDDQ_10), SDRAM4.R7 (VDD_4), U2.8 (VCC)
GND: C1.1, C2.2, C3.2, C4.2, C5.2, C6.2, C7.2, C8.2, C9.2, C10.2, C11.2, C12.2, C13.2, C14.2, C15.2, C16.2, C17.2, C18.2, C19.2, C20.2, C21.2, C22.2, C23.2, C24.2, C25.2, C26.2, C27.2, C28.2, C29.2, C30.2, C31.2, C32.2, C33.2, C34.2, C35.2, C36.2, C37.2, C38.2, C39.2, C40.2, C41.2, C42.2, C43.2, C44.2, C45.2, C46.2, C47.2, C48.2, C49.2, C50.2, C51.2, C52.2, C53.2, C54.2, C55.2, C56.2, C57.2, C58.2, C59.2, C60.2, C61.2, SDRAM1.A3 (VSS_1), SDRAM1.B3 (VSSQ_1), SDRAM1.B8 (VSSQ_2), SDRAM1.C1 (VSSQ_3), SDRAM1.D1 (VSSQ_4), SDRAM1.E9 (VSSQ_5), SDRAM1.F1 (VSS_2), SDRAM1.L3 (VSS_3), SDRAM1.L9 (VSSQ_6), SDRAM1.M1 (VSSQ_7), SDRAM1.N1 (VSSQ_8), SDRAM1.P3 (VSSQ_9), SDRAM1.P8 (VSSQ_10), SDRAM1.R3 (VSS_4), SDRAM2.A3 (VSS_1), SDRAM2.B3 (VSSQ_1), SDRAM2.B8 (VSSQ_2), SDRAM2.C1 (VSSQ_3), SDRAM2.D1 (VSSQ_4), SDRAM2.E9 (VSSQ_5), SDRAM2.F1 (VSS_2), SDRAM2.L3 (VSS_3), SDRAM2.L9 (VSSQ_6), SDRAM2.M1 (VSSQ_7), SDRAM2.N1 (VSSQ_8), SDRAM2.P3 (VSSQ_9), SDRAM2.P8 (VSSQ_10), SDRAM2.R3 (VSS_4), SDRAM3.A3 (VSS_1), SDRAM3.B3 (VSSQ_1), SDRAM3.B8 (VSSQ_2), SDRAM3.C1 (VSSQ_3), SDRAM3.D1 (VSSQ_4), SDRAM3.E9 (VSSQ_5), SDRAM3.F1 (VSS_2), SDRAM3.L3 (VSS_3), SDRAM3.L9 (VSSQ_6), SDRAM3.M1 (VSSQ_7), SDRAM3.N1 (VSSQ_8), SDRAM3.P3 (VSSQ_9), SDRAM3.P8 (VSSQ_10), SDRAM3.R3 (VSS_4), SDRAM4.A3 (VSS_1), SDRAM4.B3 (VSSQ_1), SDRAM4.B8 (VSSQ_2), SDRAM4.C1 (VSSQ_3), SDRAM4.D1 (VSSQ_4), SDRAM4.E9 (VSSQ_5), SDRAM4.F1 (VSS_2), SDRAM4.L3 (VSS_3), SDRAM4.L9 (VSSQ_6), SDRAM4.M1 (VSSQ_7), SDRAM4.N1 (VSSQ_8), SDRAM4.P3 (VSSQ_9), SDRAM4.P8 (VSSQ_10), SDRAM4.R3 (VSS_4), Shield1.1, Shield2.1, Shield3.1, Shield4.1, U2.4 (GND)
MCU_A0: R5.1
MCU_A1: R6.1
MCU_A2: R7.1
MCU_A3: R8.1
MCU_A4: R9.1
MCU_A5: R10.1
MCU_A6: R11.1
MCU_A7: R12.1
MCU_A8: R13.1
MCU_A9: R14.1
MCU_A10: R15.1
MCU_A11: R16.1
MCU_A12: R17.1
MCU_BA0: R18.1
MCU_BA1: R19.1
MCU_D0: R33.1
MCU_D1: R34.1
MCU_D2: R35.1
MCU_D3: R36.1
MCU_D4: R37.1
MCU_D5: R38.1
MCU_D6: R39.1
MCU_D7: R40.1
MCU_D8: R41.1
MCU_D9: R42.1
MCU_D10: R43.1
MCU_D11: R44.1
MCU_D12: R45.1
MCU_D13: R46.1
MCU_D14: R47.1
MCU_D15: R48.1
MCU_D16: R49.1
MCU_D17: R50.1
MCU_D18: R51.1
MCU_D19: R52.1
MCU_D20: R53.1
MCU_D21: R54.1
MCU_D22: R55.1
MCU_D23: R56.1
MCU_D24: R57.1
MCU_D25: R58.1
MCU_D26: R59.1
MCU_D27: R60.1
MCU_D28: R61.1
MCU_D29: R62.1
MCU_D30: R63.1
MCU_D31: R64.1
MCU_NBL0: R25.1
MCU_NBL1: R26.1
MCU_NBL2: R27.1
MCU_NBL3: R28.1
MCU_SDCKE1: R23.1
MCU_SDCLK: R24.1
MCU_SDNCAS: R21.1
MCU_SDNRAS: R22.1
MCU_SDNWE: R20.1
unnamed: D1.2 (A), R29.2
unnamed: D2.2 (A), R30.2
unnamed: D3.2 (A), R31.2
unnamed: D4.2 (A), R32.2
SDRAM_A0: R5.2, SDRAM1.G8 (A0), SDRAM2.G8 (A0), SDRAM3.G8 (A0), SDRAM4.G8 (A0)
SDRAM_A1: R6.2, SDRAM1.G9 (A1), SDRAM2.G9 (A1), SDRAM3.G9 (A1), SDRAM4.G9 (A1)
SDRAM_A2: R7.2, SDRAM1.F7 (A2), SDRAM2.F7 (A2), SDRAM3.F7 (A2), SDRAM4.F7 (A2)
SDRAM_A3: R8.2, SDRAM1.F3 (A3), SDRAM2.F3 (A3), SDRAM3.F3 (A3), SDRAM4.F3 (A3)
SDRAM_A4: R9.2, SDRAM1.G1 (A4), SDRAM2.G1 (A4), SDRAM3.G1 (A4), SDRAM4.G1 (A4)
SDRAM_A5: R10.2, SDRAM1.G2 (A5), SDRAM2.G2 (A5), SDRAM3.G2 (A5), SDRAM4.G2 (A5)
SDRAM_A6: R11.2, SDRAM1.G3 (A6), SDRAM2.G3 (A6), SDRAM3.G3 (A6), SDRAM4.G3 (A6)
SDRAM_A7: R12.2, SDRAM1.H1 (A7), SDRAM2.H1 (A7), SDRAM3.H1 (A7), SDRAM4.H1 (A7)
SDRAM_A8: R13.2, SDRAM1.H2 (A8), SDRAM2.H2 (A8), SDRAM3.H2 (A8), SDRAM4.H2 (A8)
SDRAM_A9: R14.2, SDRAM1.J3 (A9), SDRAM2.J3 (A9), SDRAM3.J3 (A9), SDRAM4.J3 (A9)
SDRAM_A10: R15.2, SDRAM1.G7 (A10), SDRAM2.G7 (A10), SDRAM3.G7 (A10), SDRAM4.G7 (A10)
SDRAM_A11: R16.2, SDRAM1.H9 (A11), SDRAM2.H9 (A11), SDRAM3.H9 (A11), SDRAM4.H9 (A11)
SDRAM_A12: R17.2, SDRAM1.H3 (A12), SDRAM2.H3 (A12), SDRAM3.H3 (A12), SDRAM4.H3 (A12)
SDRAM_BA0: R18.2, SDRAM1.J7 (BA0), SDRAM2.J7 (BA0), SDRAM3.J7 (BA0), SDRAM4.J7 (BA0)
SDRAM_BA1: R19.2, SDRAM1.H8 (BA1), SDRAM2.H8 (BA1), SDRAM3.H8 (BA1), SDRAM4.H8 (BA1)
SDRAM_CS0: D1.1 (K), SDRAM2.J8 (~CS), U2.3 (Y3)
SDRAM_CS1: D2.1 (K), SDRAM3.J8 (~CS), U2.5 (Y2)
SDRAM_CS2: D3.1 (K), SDRAM4.J8 (~CS), U2.6 (Y1)
SDRAM_CS3: D4.1 (K), SDRAM1.J8 (~CS), U2.7 (Y0)
SDRAM_CS_A0: U2.1 (A)
SDRAM_CS_A1: U2.2 (B)
SDRAM_D0: R33.2, SDRAM1.R8 (DQ0), SDRAM2.R8 (DQ0), SDRAM3.R8 (DQ0), SDRAM4.R8 (DQ0)
SDRAM_D1: R34.2, SDRAM1.N7 (DQ1), SDRAM2.N7 (DQ1), SDRAM3.N7 (DQ1), SDRAM4.N7 (DQ1)
SDRAM_D2: R35.2, SDRAM1.R9 (DQ2), SDRAM2.R9 (DQ2), SDRAM3.R9 (DQ2), SDRAM4.R9 (DQ2)
SDRAM_D3: R36.2, SDRAM1.N8 (DQ3), SDRAM2.N8 (DQ3), SDRAM3.N8 (DQ3), SDRAM4.N8 (DQ3)
SDRAM_D4: R37.2, SDRAM1.P9 (DQ4), SDRAM2.P9 (DQ4), SDRAM3.P9 (DQ4), SDRAM4.P9 (DQ4)
SDRAM_D5: R38.2, SDRAM1.M8 (DQ5), SDRAM2.M8 (DQ5), SDRAM3.M8 (DQ5), SDRAM4.M8 (DQ5)
SDRAM_D6: R39.2, SDRAM1.M7 (DQ6), SDRAM2.M7 (DQ6), SDRAM3.M7 (DQ6), SDRAM4.M7 (DQ6)
SDRAM_D7: R40.2, SDRAM1.L8 (DQ7), SDRAM2.L8 (DQ7), SDRAM3.L8 (DQ7), SDRAM4.L8 (DQ7)
SDRAM_D8: R41.2, SDRAM1.L2 (DQ8), SDRAM2.L2 (DQ8), SDRAM3.L2 (DQ8), SDRAM4.L2 (DQ8)
SDRAM_D9: R42.2, SDRAM1.M3 (DQ9), SDRAM2.M3 (DQ9), SDRAM3.M3 (DQ9), SDRAM4.M3 (DQ9)
SDRAM_D10: R43.2, SDRAM1.M2 (DQ10), SDRAM2.M2 (DQ10), SDRAM3.M2 (DQ10), SDRAM4.M2 (DQ10)
SDRAM_D11: R44.2, SDRAM1.P1 (DQ11), SDRAM2.P1 (DQ11), SDRAM3.P1 (DQ11), SDRAM4.P1 (DQ11)
SDRAM_D12: R45.2, SDRAM1.N2 (DQ12), SDRAM2.N2 (DQ12), SDRAM3.N2 (DQ12), SDRAM4.N2 (DQ12)
SDRAM_D13: R46.2, SDRAM1.R1 (DQ13), SDRAM2.R1 (DQ13), SDRAM3.R1 (DQ13), SDRAM4.R1 (DQ13)
SDRAM_D14: R47.2, SDRAM1.N3 (DQ14), SDRAM2.N3 (DQ14), SDRAM3.N3 (DQ14), SDRAM4.N3 (DQ14)
SDRAM_D15: R48.2, SDRAM1.R2 (DQ15), SDRAM2.R2 (DQ15), SDRAM3.R2 (DQ15), SDRAM4.R2 (DQ15)
SDRAM_D16: R49.2, SDRAM1.E8 (DQ16), SDRAM2.E8 (DQ16), SDRAM3.E8 (DQ16), SDRAM4.E8 (DQ16)
SDRAM_D17: R50.2, SDRAM1.D7 (DQ17), SDRAM2.D7 (DQ17), SDRAM3.D7 (DQ17), SDRAM4.D7 (DQ17)
SDRAM_D18: R51.2, SDRAM1.D8 (DQ18), SDRAM2.D8 (DQ18), SDRAM3.D8 (DQ18), SDRAM4.D8 (DQ18)
SDRAM_D19: R52.2, SDRAM1.B9 (DQ19), SDRAM2.B9 (DQ19), SDRAM3.B9 (DQ19), SDRAM4.B9 (DQ19)
SDRAM_D20: R53.2, SDRAM1.C8 (DQ20), SDRAM2.C8 (DQ20), SDRAM3.C8 (DQ20), SDRAM4.C8 (DQ20)
SDRAM_D21: R54.2, SDRAM1.A9 (DQ21), SDRAM2.A9 (DQ21), SDRAM3.A9 (DQ21), SDRAM4.A9 (DQ21)
SDRAM_D22: R55.2, SDRAM1.C7 (DQ22), SDRAM2.C7 (DQ22), SDRAM3.C7 (DQ22), SDRAM4.C7 (DQ22)
SDRAM_D23: R56.2, SDRAM1.A8 (DQ23), SDRAM2.A8 (DQ23), SDRAM3.A8 (DQ23), SDRAM4.A8 (DQ23)
SDRAM_D24: R57.2, SDRAM1.A2 (DQ24), SDRAM2.A2 (DQ24), SDRAM3.A2 (DQ24), SDRAM4.A2 (DQ24)
SDRAM_D25: R58.2, SDRAM1.C3 (DQ25), SDRAM2.C3 (DQ25), SDRAM3.C3 (DQ25), SDRAM4.C3 (DQ25)
SDRAM_D26: R59.2, SDRAM1.A1 (DQ26), SDRAM2.A1 (DQ26), SDRAM3.A1 (DQ26), SDRAM4.A1 (DQ26)
SDRAM_D27: R60.2, SDRAM1.C2 (DQ27), SDRAM2.C2 (DQ27), SDRAM3.C2 (DQ27), SDRAM4.C2 (DQ27)
SDRAM_D28: R61.2, SDRAM1.B1 (DQ28), SDRAM2.B1 (DQ28), SDRAM3.B1 (DQ28), SDRAM4.B1 (DQ28)
SDRAM_D29: R62.2, SDRAM1.D2 (DQ29), SDRAM2.D2 (DQ29), SDRAM3.D2 (DQ29), SDRAM4.D2 (DQ29)
SDRAM_D30: R63.2, SDRAM1.D3 (DQ30), SDRAM2.D3 (DQ30), SDRAM3.D3 (DQ30), SDRAM4.D3 (DQ30)
SDRAM_D31: R64.2, SDRAM1.E2 (DQ31), SDRAM2.E2 (DQ31), SDRAM3.E2 (DQ31), SDRAM4.E2 (DQ31)
SDRAM_NBL0: R25.2, SDRAM1.K9 (DQM0), SDRAM2.K9 (DQM0), SDRAM3.K9 (DQM0), SDRAM4.K9 (DQM0)
SDRAM_NBL1: R26.2, SDRAM1.K1 (DQM1), SDRAM2.K1 (DQM1), SDRAM3.K1 (DQM1), SDRAM4.K1 (DQM1)
SDRAM_NBL2: R27.2, SDRAM1.F8 (DQM2), SDRAM2.F8 (DQM2), SDRAM3.F8 (DQM2), SDRAM4.F8 (DQM2)
SDRAM_NBL3: R28.2, SDRAM1.F2 (DQM3), SDRAM2.F2 (DQM3), SDRAM3.F2 (DQM3), SDRAM4.F2 (DQM3)
SDRAM_SDCKE1: R23.2, SDRAM1.J2 (CKE), SDRAM2.J2 (CKE), SDRAM3.J2 (CKE), SDRAM4.J2 (CKE)
SDRAM_SDCLK: R24.2, SDRAM1.J1 (CLK), SDRAM2.J1 (CLK), SDRAM3.J1 (CLK), SDRAM4.J1 (CLK)
SDRAM_SDNCAS: R21.2, SDRAM1.K7 (~CAS), SDRAM2.K7 (~CAS), SDRAM3.K7 (~CAS), SDRAM4.K7 (~CAS)
SDRAM_SDNRAS: R22.2, SDRAM1.J9 (~RAS), SDRAM2.J9 (~RAS), SDRAM3.J9 (~RAS), SDRAM4.J9 (~RAS)
SDRAM_SDNWE: R20.2, SDRAM1.K8 (~WE), SDRAM2.K8 (~WE), SDRAM3.K8 (~WE), SDRAM4.K8 (~WE)

Notes on the sheet:
SDRAM 1
Damping Resistors
SDRAM 3
SDRAM 2
SDRAM 4
